simplexjunkie/meetstatief/STL bestanden/Eindstuk 2 met 2 draaipunten voor aluminium 20x20x1,5 V3.stl

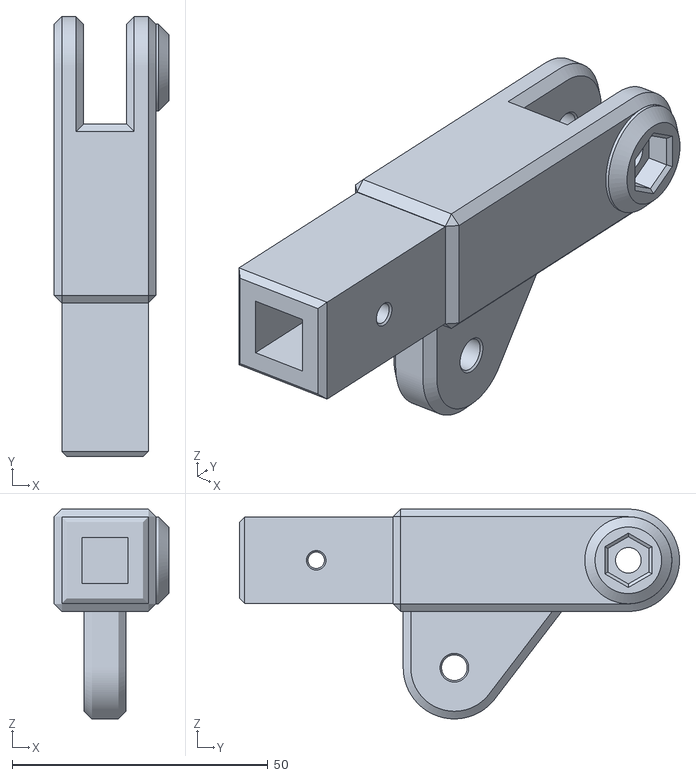
[picture p19: CAD file, 2021-11-30]
STL bestanden/Eindstuk 2 met 2 draaipunten voor aluminium 20x20x1,5 V3.stl
22.4 x 86.0 x 41.0
